JoshGinnett/Audio-Amplifier-and-Speaker-Design/ltspice/20250907- Project 1 - Final.asc

2.4k: res; 2.4k
C1: cap; 10µF
C2: cap; 470µF
C3: cap; 1µ
C4: cap; 4700µF
C5: cap; 470µF
C6: cap; 33µF
C7: cap; 33µF
C9: cap; 1µF
C18: cap; 100n
C19: cap; 33µ
C20: cap; 100n
C21: cap; 33µ
D1: diode
D2: diode
D3: diode
D4: diode
D5: diode
D6: diode
D7: diode
D8: diode
D9: LED
D10: LED
D12: diode; 1N4148
D13: diode; 1N4148
NE1: UniversalOpAmp2; Ilimit=70m Rail=0 Vos=0
NE5532P-2: UniversalOpAmp2; Ilimit=70m Rail=0 Vos=0
NE5532P: UniversalOpAmp2; Ilimit=70m Rail=0 Vos=0
OpAmp2: UniversalOpAmp2; Ilimit=70m Rail=0 Vos=0
OpAmp3: UniversalOpAmp2; Ilimit=70m Rail=0 Vos=0
OpAmp4: UniversalOpAmp2; Ilimit=70m Rail=0 Vos=0
OpAmp6: UniversalOpAmp2; Ilimit=70m Rail=0 Vos=0
OpAmp7: UniversalOpAmp2; Ilimit=70m Rail=0 Vos=0
OpAmp8: UniversalOpAmp2; Ilimit=70m Rail=0 Vos=0
OpAmp9: UniversalOpAmp2; Ilimit=70m Rail=0 Vos=0
OpAmp10: UniversalOpAmp2; Ilimit=70m Rail=0 Vos=0
OpAmp11: UniversalOpAmp2; Ilimit=70m Rail=0 Vos=0
OpAmp12: UniversalOpAmp2; Ilimit=70m Rail=0 Vos=0
OpAmp13: UniversalOpAmp2; Ilimit=70m Rail=0 Vos=0
Q1: npn; mynpn
Q2: pnp; mypnp
R1: res; .33
R2: res; .33
R3: res; 560
R4: res; 100
R5: res; 9.9k
R6: res; 1k
R7: res; 2.4k
R8: res; 0.33
R9: res; 560
R10: res; 10k
R11: res; 100
R12: res; 1k
R13: res; 0.33
R14: res; 10k
R15: res; 10k
R16: res; 560
R23: res; 1k
R24: res; 1K
R26: res; 560
R27: res; 560
R29: res; 560
R30: res; 560
R31: res; 560
R32: res; 560
R33: res; 560
R34: res; 560
R35: res; 1K
R36: res; 1K
R37: res; 1K
R38: res; 1K
R39: res; 1K
R40: res; 1K
R41: res; 1K
R42: res; 10k
R46: res; 1k
Rf: res; 4.7k
Speaker: res; 8
V1: voltage; SINE(0 1.5V 1.5k)
V2: voltage; 9v
V3: voltage; 4.5
V4: voltage; 4.5
V6: voltage; SINE(1 0.5V 5Khz)
Named nets: AuxSig, 0, Vcc+, Vcc-, out, PhotoSig, vcc-
.tran 15s
Power Source (2 Series 9V Battery -> +- 9V)
8 Level LED Output Indicator
Laser Output 2
Measured Aux Signal: VPeak = 1.5V, Vrms = 0.9899
Measured Solar Cell Output from Laser: Vpeak = 500mV, Vrms = 0.35355
Amplifier
Input Vpeak = 1.5V -> Output = 4.5V for 2.53W Peak, needed gain Av = 3
Volume Pot 10k
Preamp for PhotoSig (due to lower output V of solarcell
.model mynpn NPN(IS=1E-14 VAF=100 BF=200 IKF=0.3 XTB=1.5 BR=3 CJC=8E-12 CJE=25E-12 TR=100E-9 TF=400E-12 ITF=1 VTF=2 XTF=3 RB=10 RC=.3 RE=.2 Vceo=80 Icrating=3 mfg=NXP)
.model mypnp PNP(IS=1E-14 VAF=100 BF=200 IKF=0.3 XTB=1.5 BR=3 CJC=8E-12 CJE=25E-12 TR=100E-9 TF=400E-12 ITF=1 VTF=2 XTF=3 RB=10 RC=.3 RE=.2 Vceo=80 Icrating=3 mfg=NXP)
Laser Output 1
Solar Cell
GND
Vcc+
Vcc-
5k pot for gain
Switch
LM358
LM358
don't have
don't have
don't have
don't have
don't have
don't have
don't have
